MohamedSharfi/STM32WB-DEV-BOARD/3DPictures/STM32Back.png

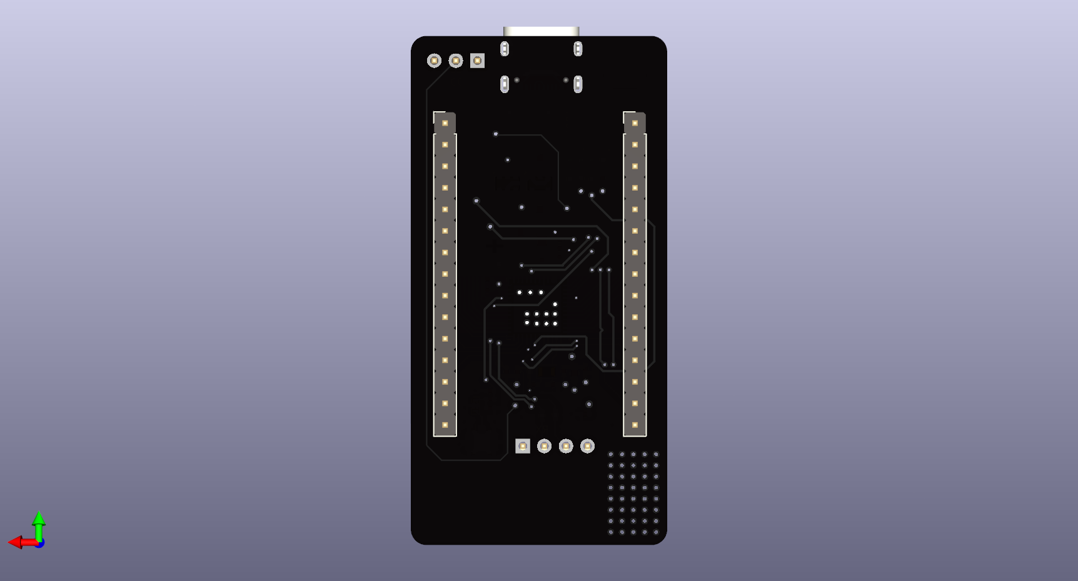
3DPictures/STM32Back.png
