MohamedSharfi/STM32WB-DEV-BOARD/3DPictures/STM32side1.png

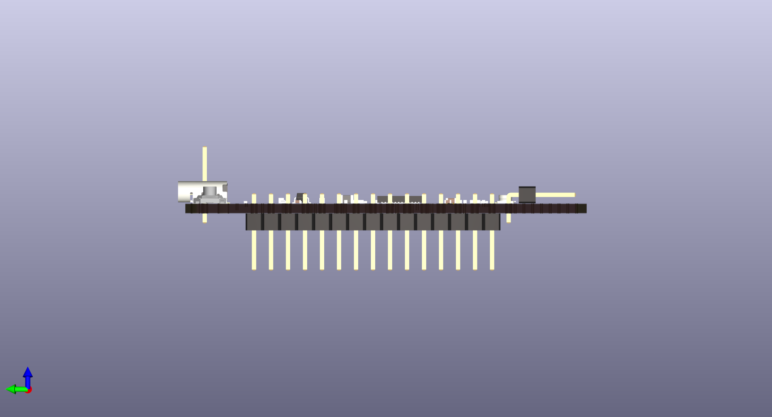
3DPictures/STM32side1.png
